ksummers92/Trident-Mods/Reaper_Toolhead_Mods/Cutter/Cutter Arm Bottom V2.step

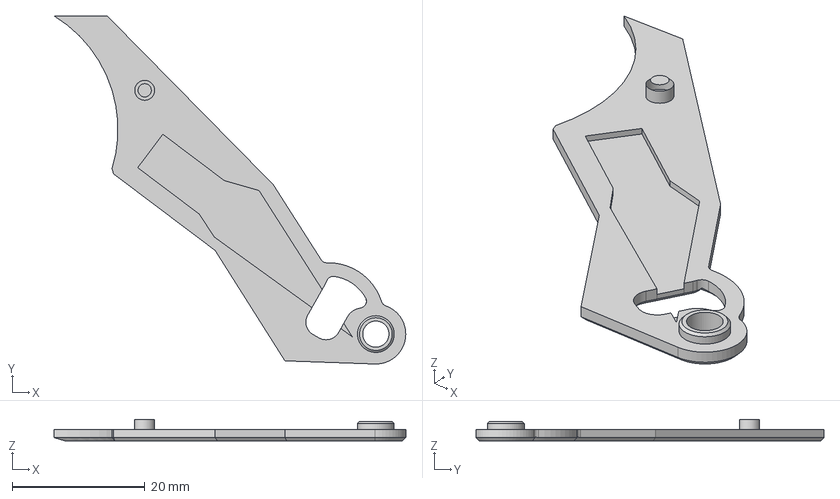
[picture p28: CAD file, 2025-03-30]
Reaper_Toolhead_Mods/Cutter/Cutter Arm Bottom V2.step
53.0 x 52.4 x 3.75 mm
