ksummers92/Trident-Mods/Reaper_Toolhead_Mods/NH36 v1.4 Mount/STL/NH36 v1.4 PG7 Mount Spacer v2.stl

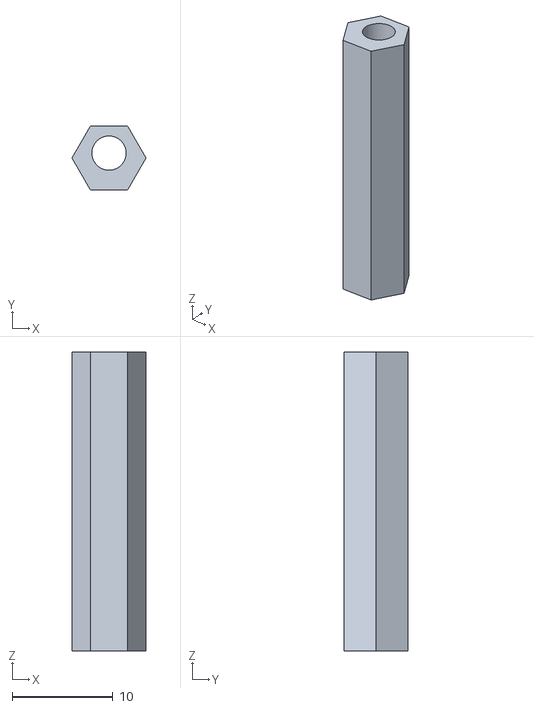
[picture p29: CAD file, 2025-03-04]
Reaper_Toolhead_Mods/NH36 v1.4 Mount/STL/NH36 v1.4 PG7 Mount Spacer v2.stl
7.36 x 6.38 x 29.7
