ksummers92/Trident-Mods/Reaper_Toolhead_Mods/NH36 v1.4 Mount/STL/NH36 v1.4 Board Cover v4.stl

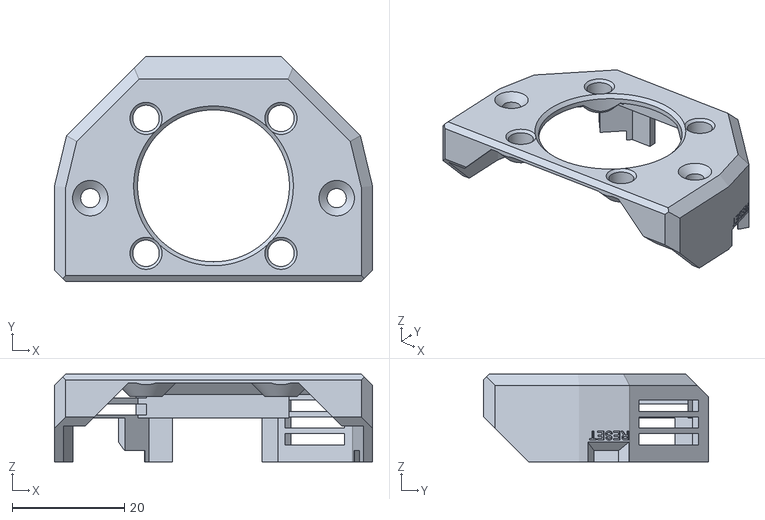
[picture p30: CAD file, 2025-03-04]
Reaper_Toolhead_Mods/NH36 v1.4 Mount/STL/NH36 v1.4 Board Cover v4.stl
56.6 x 40.0 x 15.6
