ksummers92/Trident-Mods/Gantry Blobifier/STLs/Blobifier Coupler.stl

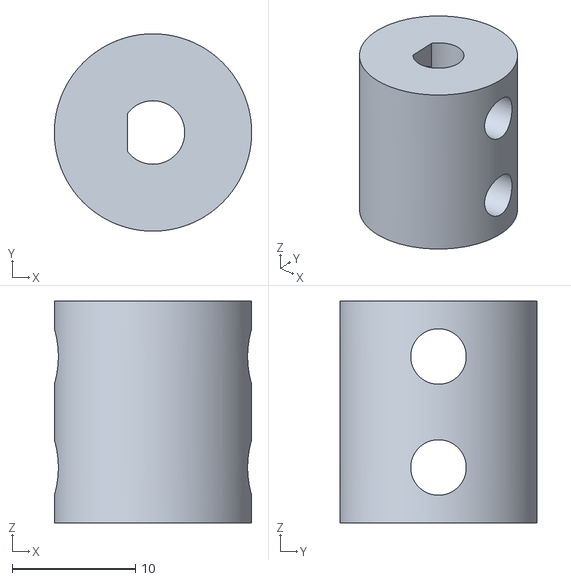
[picture p31: CAD file, 2025-02-20]
Gantry Blobifier/STLs/Blobifier Coupler.stl
16.0 x 16.0 x 18.0
