ksummers92/Trident-Mods/Gantry Blobifier/STLs/Stepper Mount - NEMA 17.stl

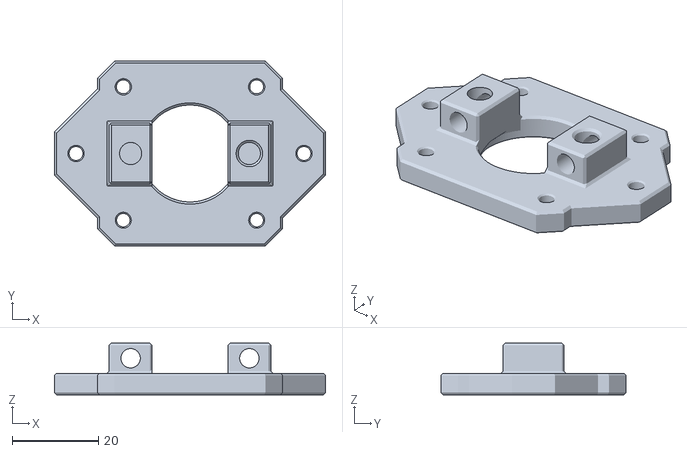
[picture p32: CAD file, 2025-02-20]
Gantry Blobifier/STLs/Stepper Mount - NEMA 17.stl
63.0 x 43.0 x 12.0
