ksummers92/Trident-Mods/Reaper_Toolhead_Mods/Cutter/Servo arm depressor.step

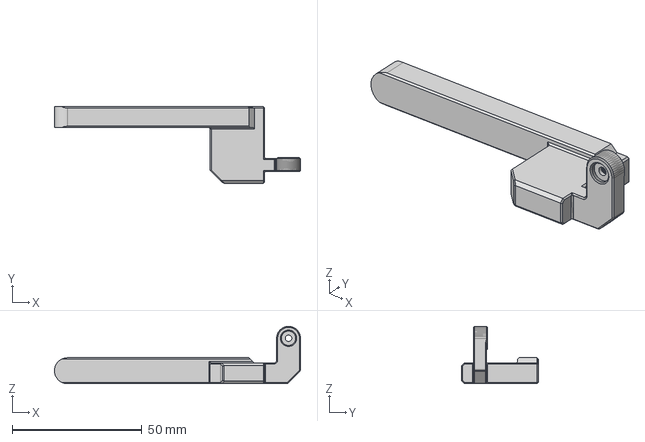
[picture p33: CAD file, 2025-02-04]
Reaper_Toolhead_Mods/Cutter/Servo arm depressor.step
94.8 x 29.5 x 22.1 mm
