ksummers92/Trident-Mods/Reaper_Toolhead_Mods/Cutter/Gantry-mounted servo.stl

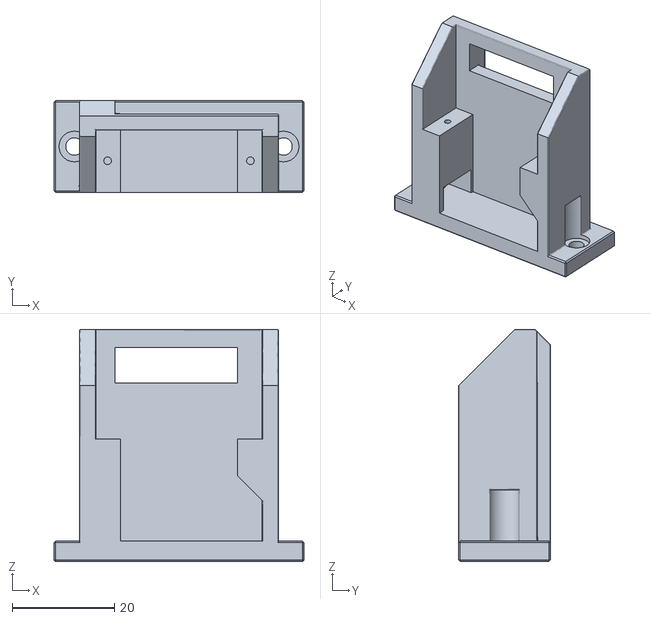
[picture p34: CAD file, 2025-01-22]
Reaper_Toolhead_Mods/Cutter/Gantry-mounted servo.stl
49.0 x 18.0 x 45.5
